bdureau/RocketMotorPIDGimbal/kalman.cpp

#include "kalman.h"

//Kalman Variables
 float f_1=1.00000;  //cast as float
 float kalman_x;
 float kalman_x_last;
 float kalman_p;
 float kalman_p_last;
 float kalman_k;
 float kalman_q;
 float kalman_r;
 float kalman_x_temp;
 float kalman_p_temp;
//end of Kalman Variables
//================================================================
// Kalman functions in your code
//================================================================

//Call KalmanInit() once.  

//KalmanInit() - Call before any iterations of KalmanCalc()
void KalmanInit()
{

  kalman_q=4.0001;  //filter parameters, you can play around with them
  kalman_r=.20001;  // but these values appear to be fairly optimal

  kalman_x = 0;
  kalman_p = 0;
  kalman_x_temp = 0;
  kalman_p_temp = 0;

  kalman_x_last = 0;
  kalman_p_last = 0;

}

//KalmanCalc() - Calculates new Kalman values from float value "altitude"
// This will be the ASL altitude during the flight, and the AGL altitude during dumps
float KalmanCalc (float altitude)
{

  //Predict kalman_x_temp, kalman_p_temp
  kalman_x_temp = kalman_x_last;
  kalman_p_temp = kalman_p_last + kalman_r;

  //Update kalman values
  kalman_k = (f_1/(kalman_p_temp + kalman_q)) * kalman_p_temp;
  kalman_x = kalman_x_temp + (kalman_k * (altitude - kalman_x_temp));
  kalman_p = (f_1 - kalman_k) * kalman_p_temp;

  //Save this state for next time
  kalman_x_last = kalman_x;
  kalman_p_last = kalman_p;

  //Assign current Kalman filtered altitude to working variables
  //KAlt = kalman_x; //FLOAT Kalman-filtered altitude value
  return kalman_x;
}  
